okmas-32/Axel/3D_models/Bimbis_V2/Gripper/Gripper link 2.stl

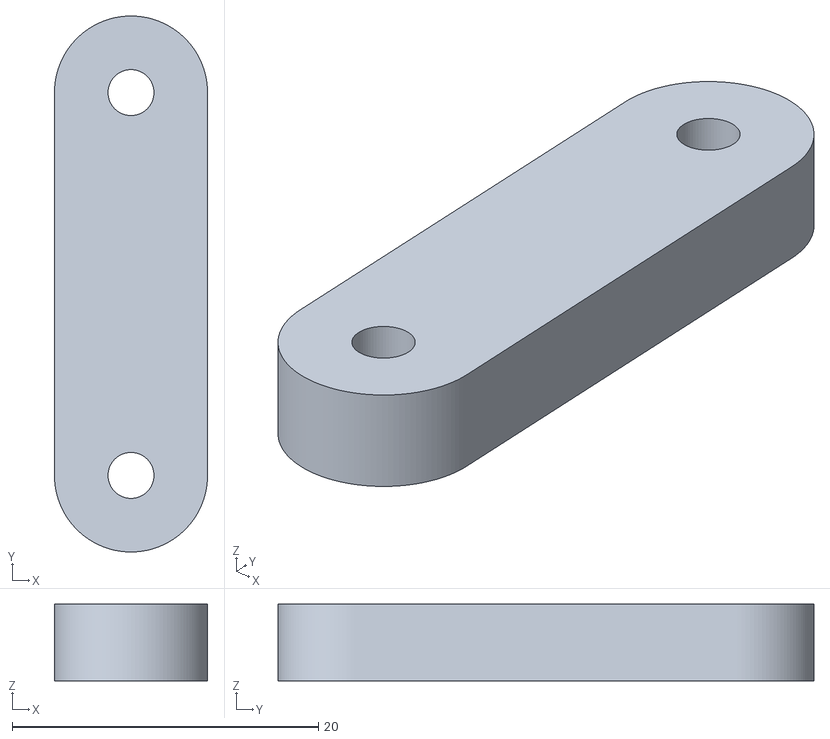
[picture p17: CAD file, 2022-02-08]
3D_models/Bimbis_V2/Gripper/Gripper link 2.stl
10.0 x 35.0 x 5.00
