okmas-32/Axel/AR-arduino/Angie_RP-AR_test/parametre.h

#ifndef PARAMETERS_H
#define PARAMETERS_H

#define debugb false
#define ARMservo true

#define serStart "Axel,Angie,"
#define space ","
#define SERIAL_BAUD 115200

// v milimetroch
#define _base "42"
#define _waist "69"
#define _arm1 "143"
#define _arm2 "96"
#define _hook "22"

//keby niekedy potrebujem na dvojitý prepočet v Arduine
#define i_base 42
#define i_waist 69
#define i_arm1 143
#define i_arm2 96
#define i_hak 75

#define sr1 3
#define sr2 5
#define sr3 9
#define sr4 11

// minimá a Maximá sierv
#define ser1max 180
#define ser1min 1

#define ser2max 180
#define ser2min 1

#define ser3max 180
#define ser3min 20

#define ser4max 180
#define ser4min 1

#endif
